Autofabricantes/H3_Henar-3/01_Documentation/H3_Flashing_04.png

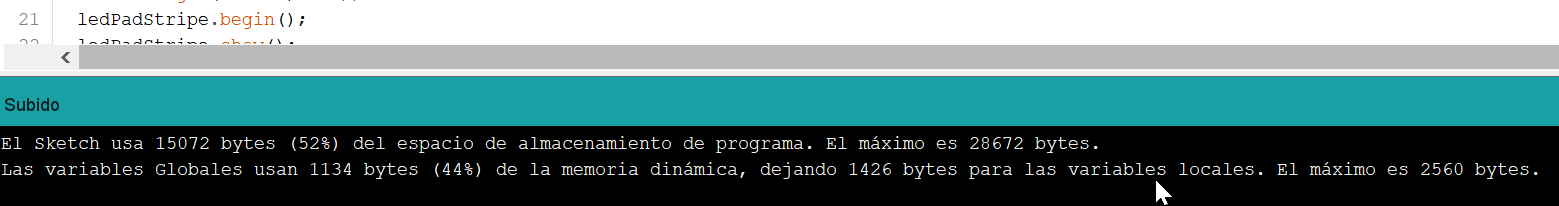
01_Documentation/H3_Flashing_04.png
