Autofabricantes/H3_Henar-3/01_Documentation/H3_Flashing_06.png

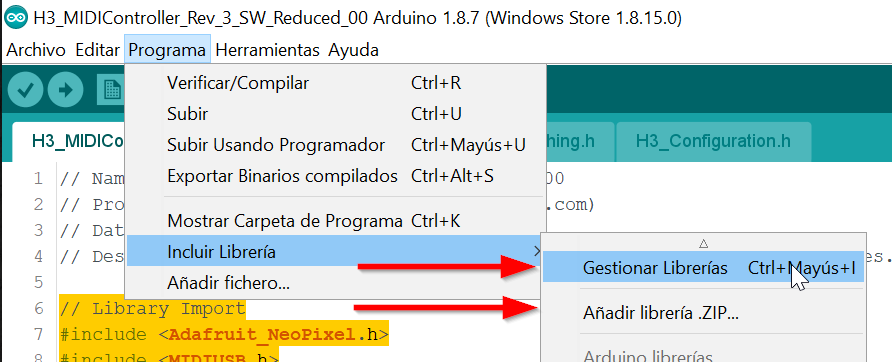
01_Documentation/H3_Flashing_06.png
