Autofabricantes/H3_Henar-3/01_Documentation/H3_REDUCED_00.png

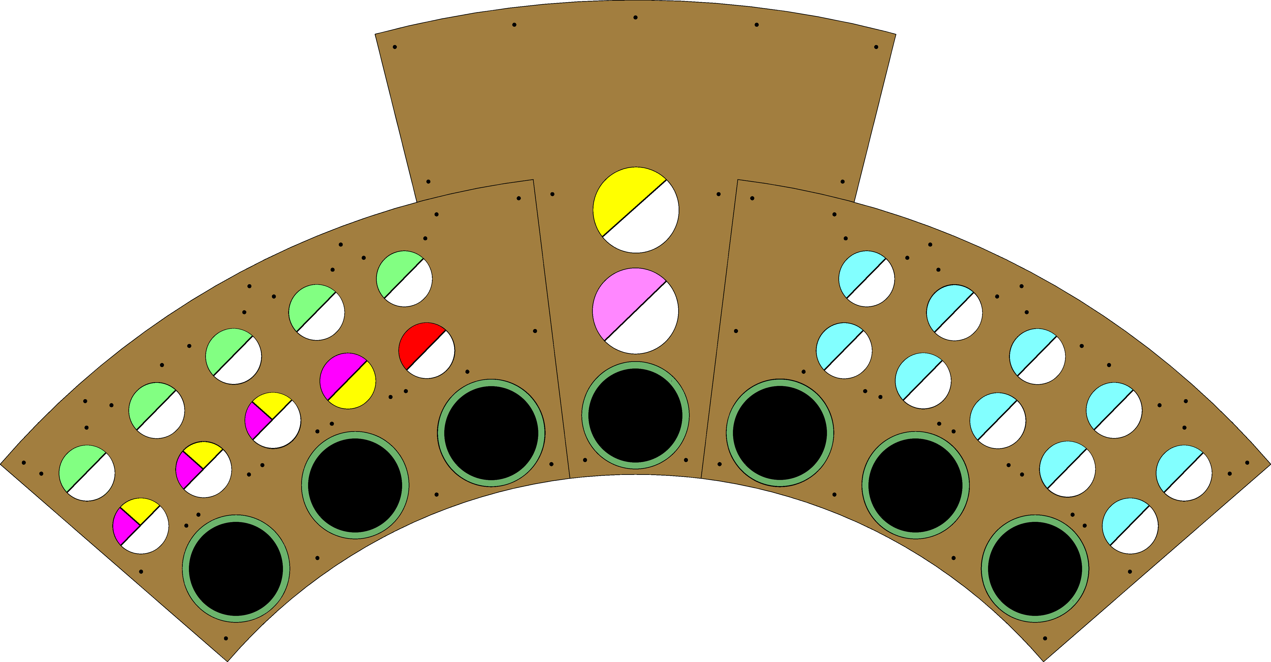
01_Documentation/H3_REDUCED_00.png
