Autofabricantes/H3_Henar-3/01_Documentation/H3_System_Rev_1_Diagram.png

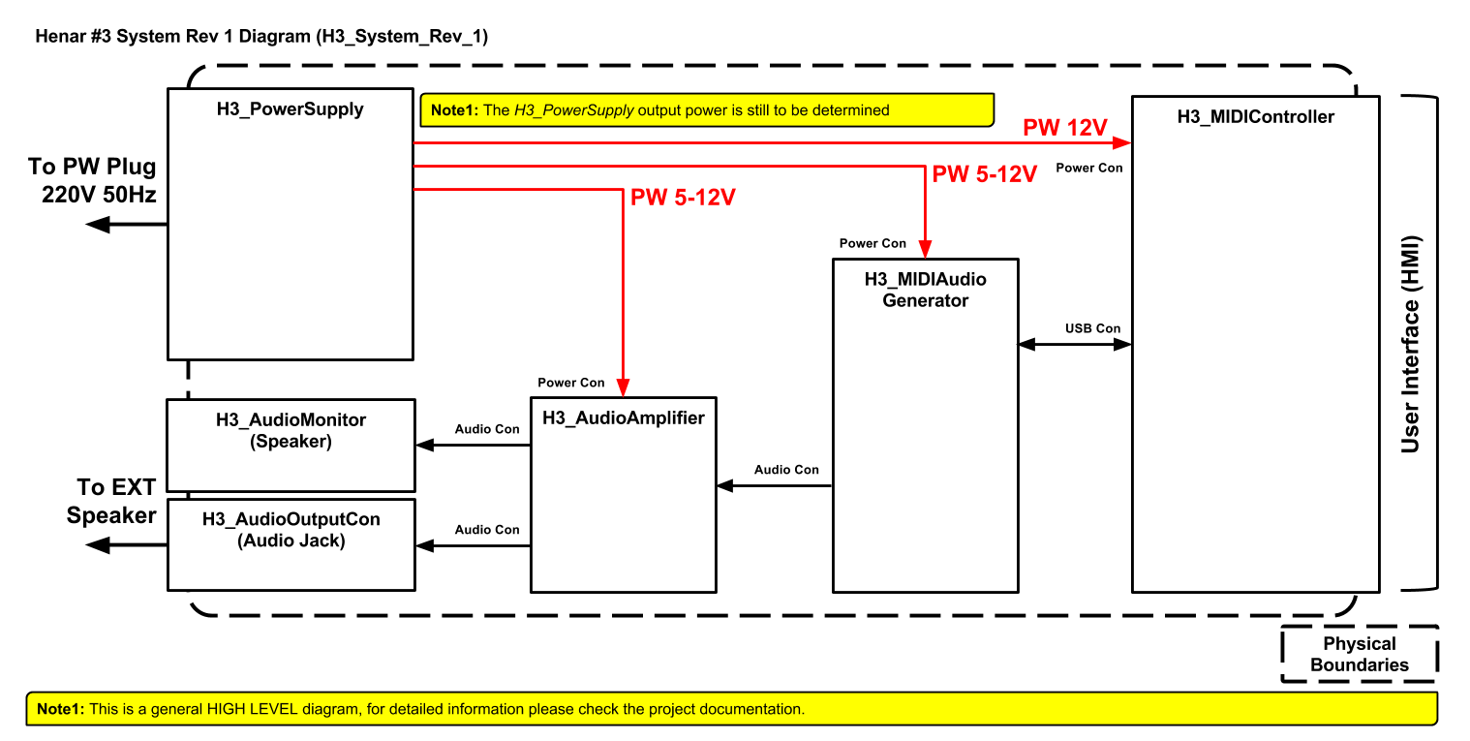
01_Documentation/H3_System_Rev_1_Diagram.png
