Autofabricantes/H3_Henar-3/02_Elements/H3_MIDISmallController_Rev_1/00_Documentation/H3_MIDISmallController_Rev_1_2DRender.png

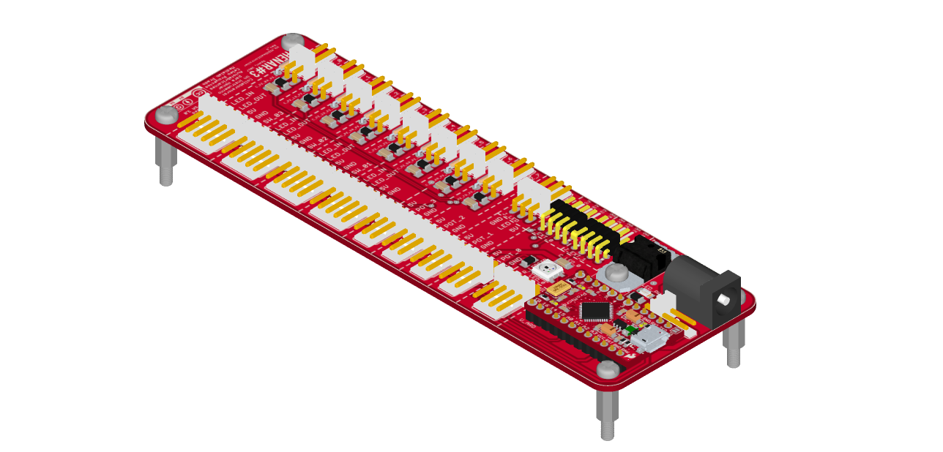
02_Elements/H3_MIDISmallController_Rev_1/00_Documentation/H3_MIDISmallController_Rev_1_2DRender.png
