Autofabricantes/H3_Henar-3/02_Elements/H3_MIDISmallController_Rev_1/01_HW/eagleUp/eagleUp_H3_MIDISmallController_Rev_1_board_top.png

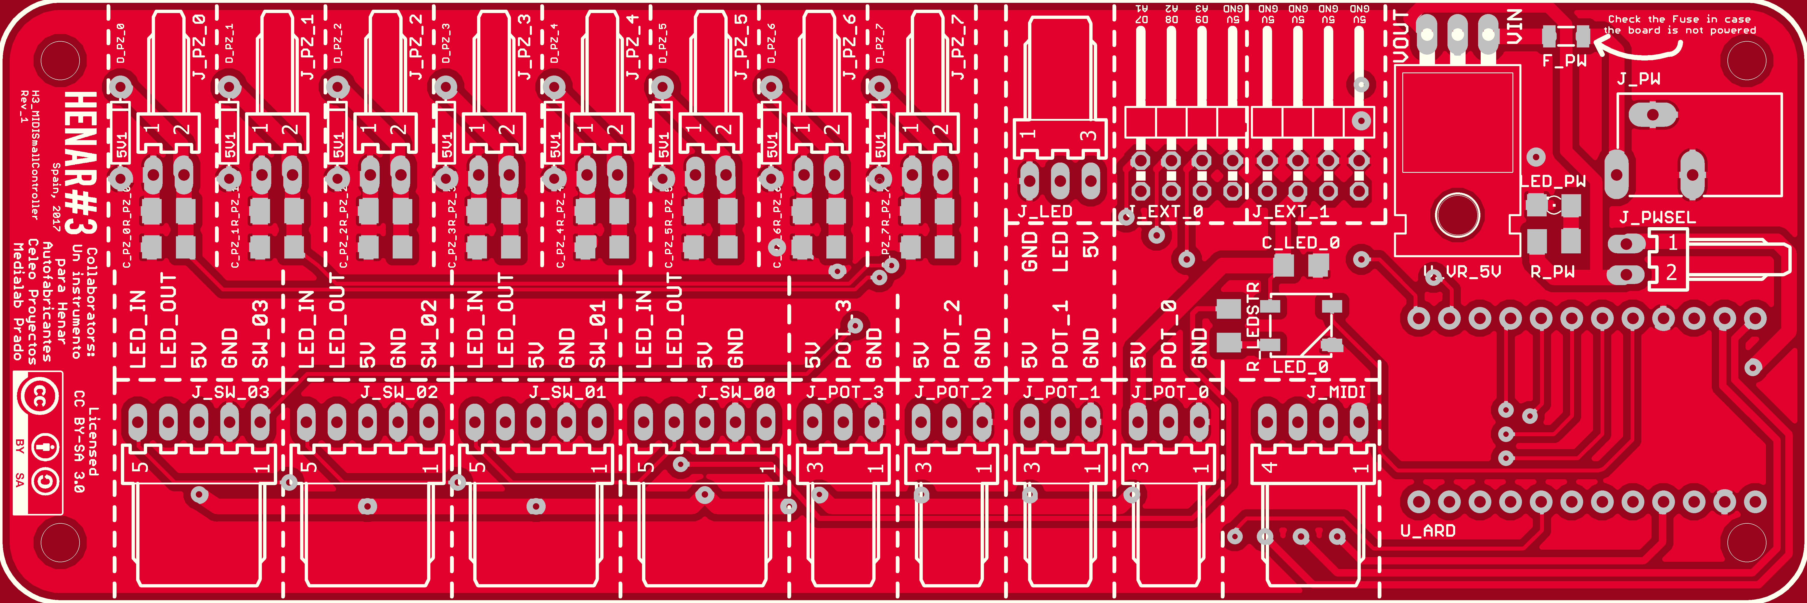
02_Elements/H3_MIDISmallController_Rev_1/01_HW/eagleUp/eagleUp_H3_MIDISmallController_Rev_1_board_top.png
