Autofabricantes/H3_Henar-3/02_Elements/H3_SWPad_Big_Rev_3/00_Documentation/H3_SWPad_Small_Rev_3_Board_Symbol.png

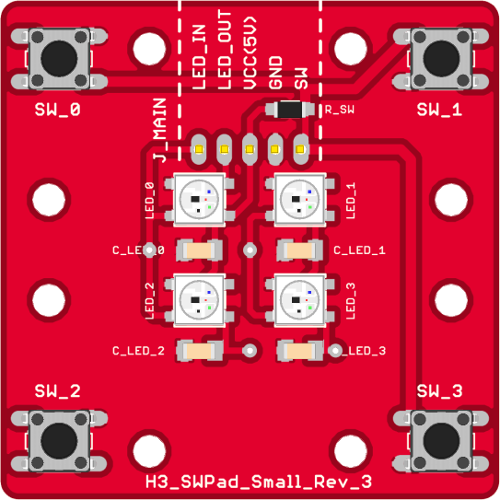
02_Elements/H3_SWPad_Big_Rev_3/00_Documentation/H3_SWPad_Small_Rev_3_Board_Symbol.png
