Autofabricantes/H3_Henar-3/02_Elements/H3_SWPad_Small_Rev_3/01_HW/eagleUp/eagleUp_H3_SWPad_Small_Rev_3_board_top.png

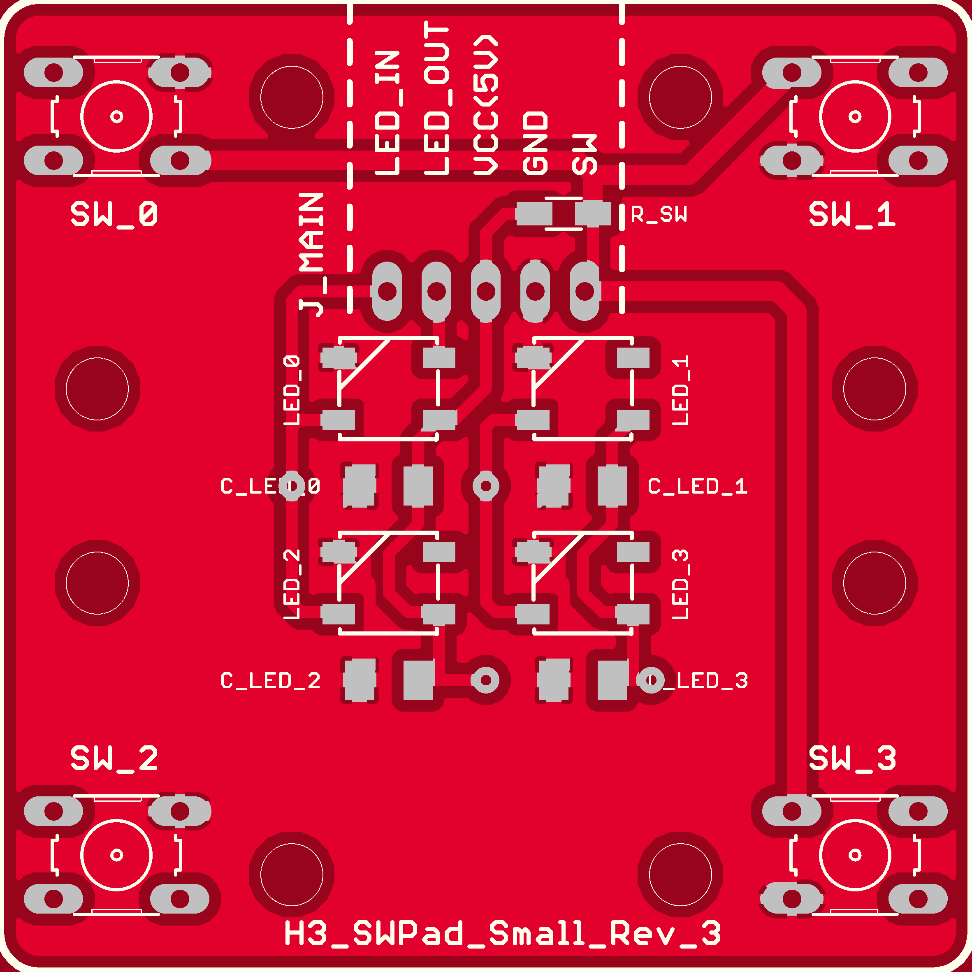
02_Elements/H3_SWPad_Small_Rev_3/01_HW/eagleUp/eagleUp_H3_SWPad_Small_Rev_3_board_top.png
