Autofabricantes/H3_Henar-3/02_Elements/H3_SWPad_Small_Rev_3/01_HW/eagleUp/eagleUp_H3_SWPad_Small_Rev_3_TopMec_board_bottom.png

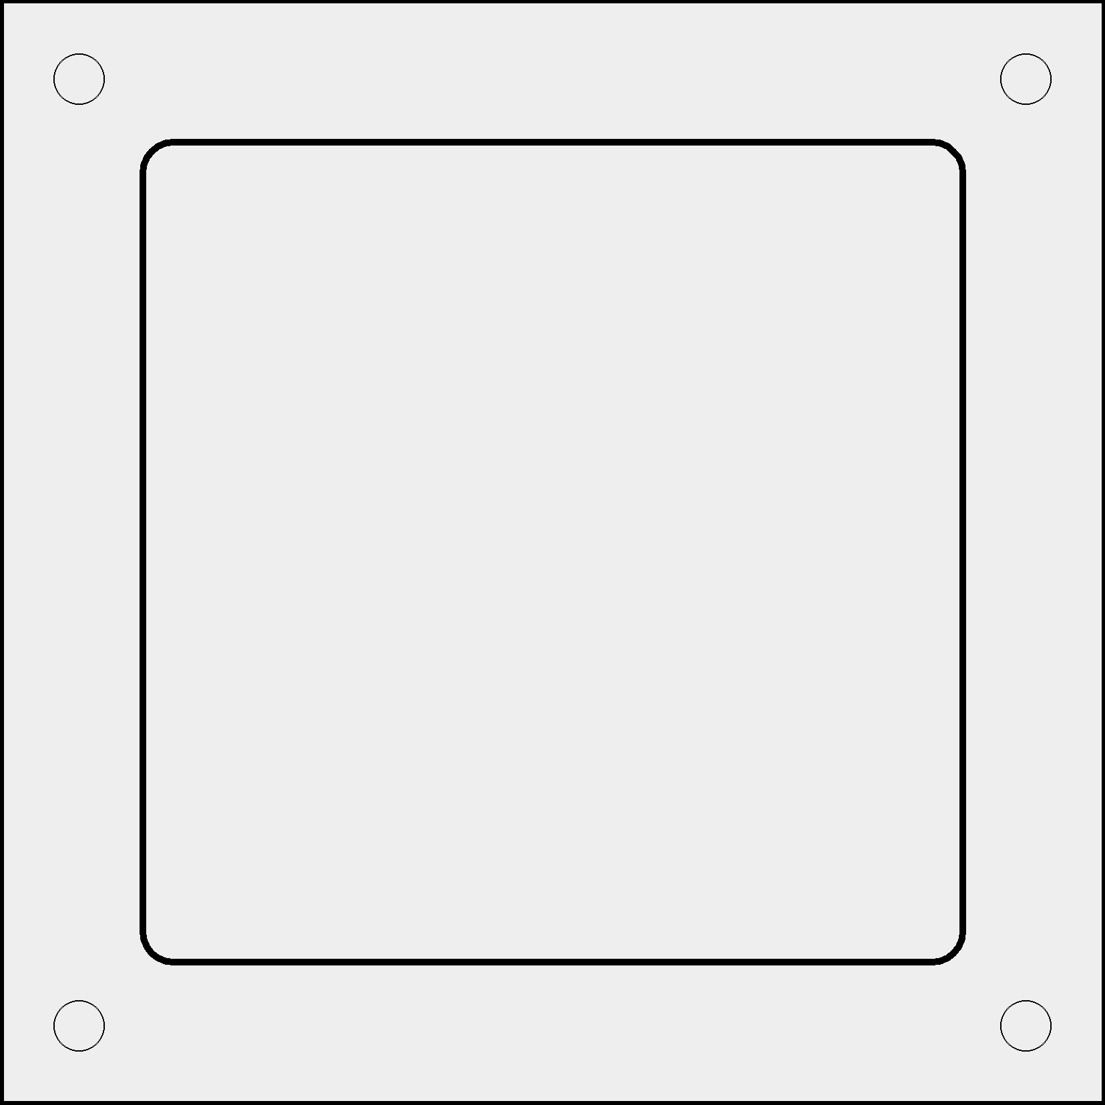
02_Elements/H3_SWPad_Small_Rev_3/01_HW/eagleUp/eagleUp_H3_SWPad_Small_Rev_3_TopMec_board_bottom.png
