Autofabricantes/H3_Henar-3/03_Resources/H3_ComponentImages/H3_MIDISmallController_Rev_1_2DRender_D.png

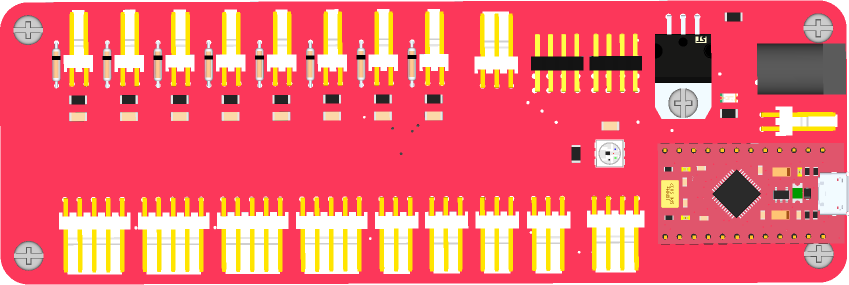
03_Resources/H3_ComponentImages/H3_MIDISmallController_Rev_1_2DRender_D.png
