Autofabricantes/H3_Henar-3/03_Resources/H3_ComponentImages/H3_POTPad_Rev_2_2DRender.png

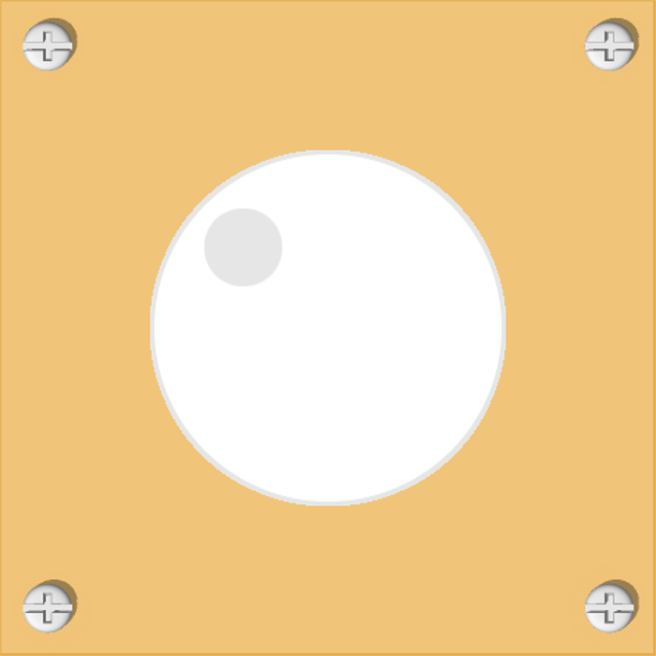
03_Resources/H3_ComponentImages/H3_POTPad_Rev_2_2DRender.png
