Autofabricantes/H3_Henar-3/03_Resources/H3_ComponentImages/H3_SWPad_Small_Rev_3_2DRender.png

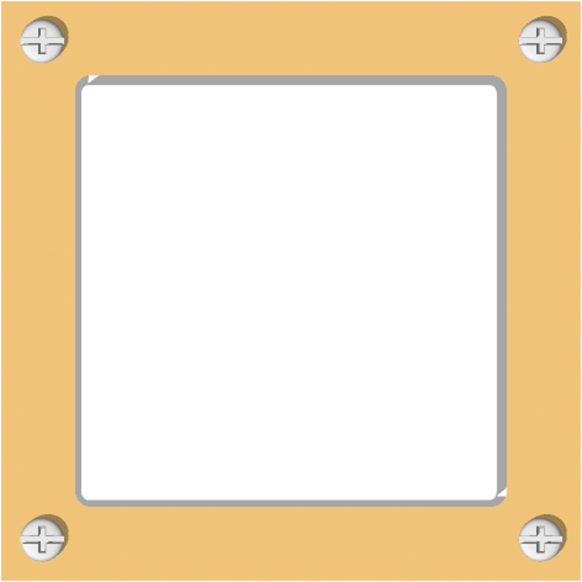
03_Resources/H3_ComponentImages/H3_SWPad_Small_Rev_3_2DRender.png
