Autofabricantes/H3_Henar-3/03_Resources/H3_ComponentImages/SensoresFull.jpg

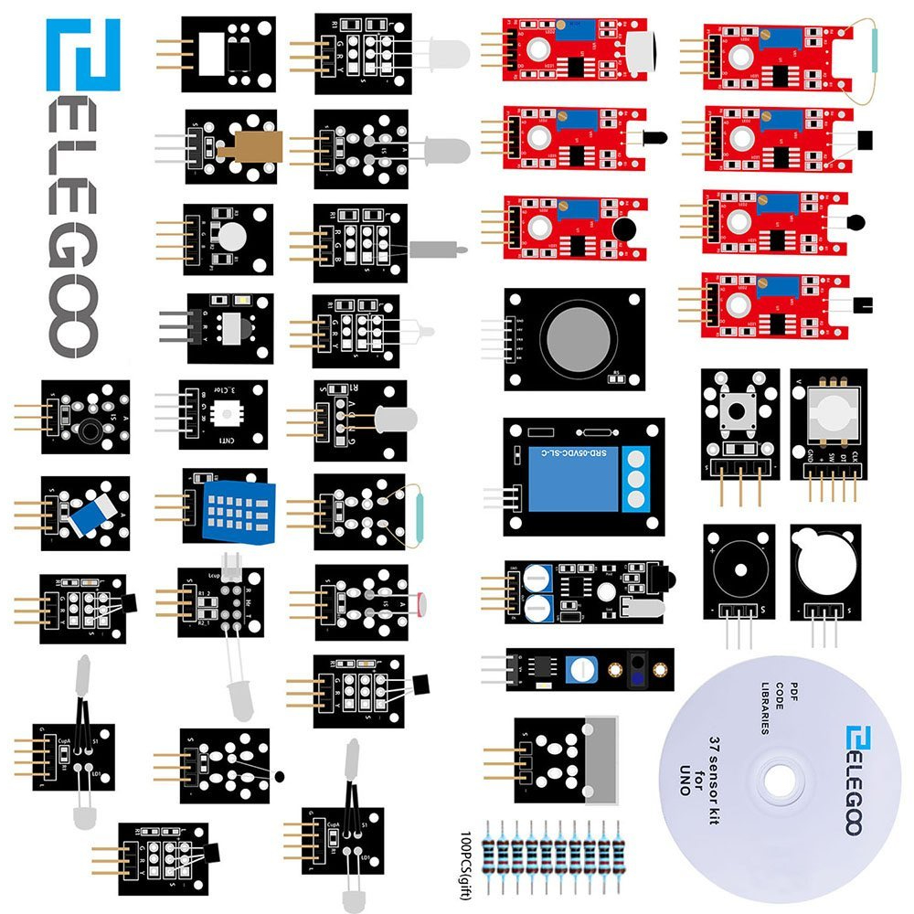
03_Resources/H3_ComponentImages/SensoresFull.jpg
