Autofabricantes/H3_Henar-3/01_Documentation/H3_GuideResources/H3_PAD_Render/H3_PAD_FRST_ON.png

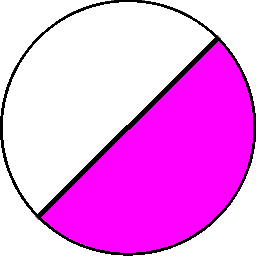
01_Documentation/H3_GuideResources/H3_PAD_Render/H3_PAD_FRST_ON.png
