Autofabricantes/H3_Henar-3/01_Documentation/H3_GuideResources/H3_SET_Render/H3_SLEEP.png

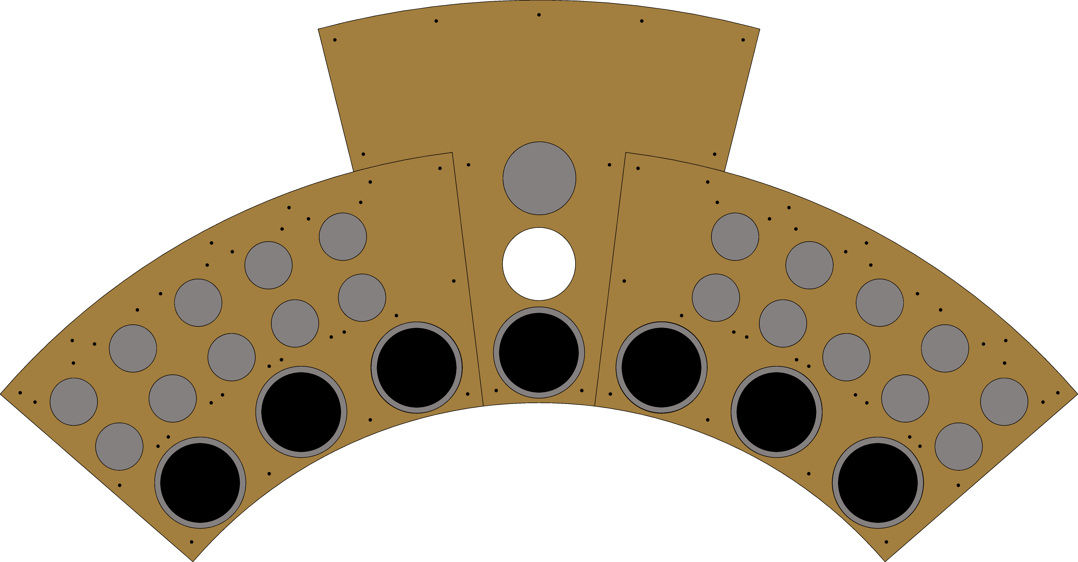
01_Documentation/H3_GuideResources/H3_SET_Render/H3_SLEEP.png
