Autofabricantes/H3_Henar-3/02_Elements/H3_VelostatPadTest/00_Documentation/H3_VelostatTest (1).png

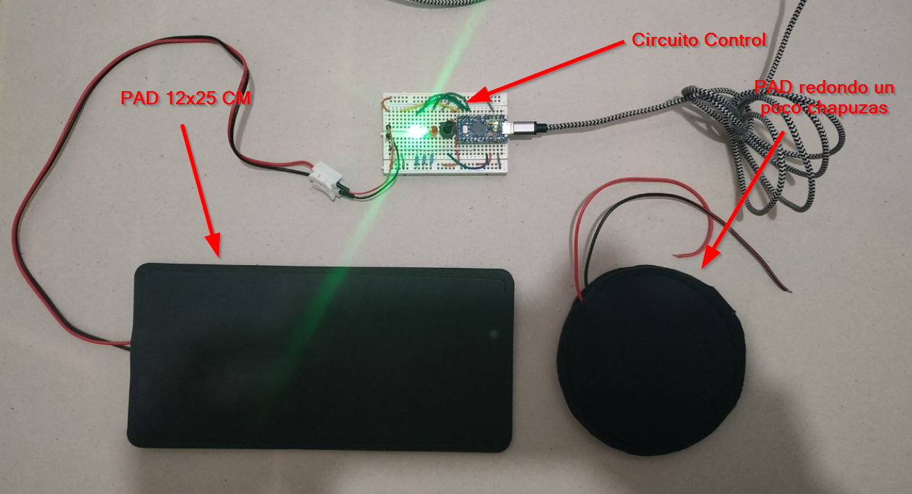
02_Elements/H3_VelostatPadTest/00_Documentation/H3_VelostatTest (1).png
