Autofabricantes/H3_Henar-3/02_Elements/H3_VelostatPadTest/00_Documentation/H3_VelostatTest (2).png

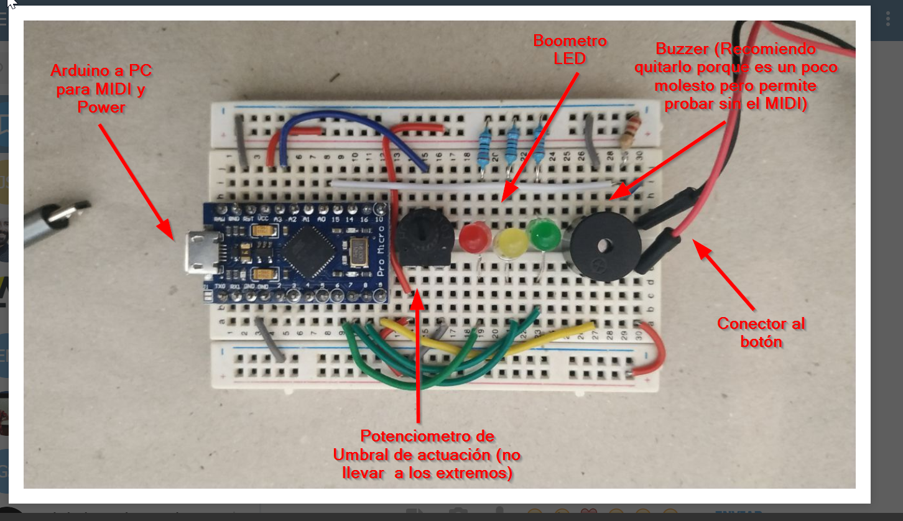
02_Elements/H3_VelostatPadTest/00_Documentation/H3_VelostatTest (2).png
