Autofabricantes/H3_Henar-3/03_Resources/H3_VelostatExperiment/H3_VelostatExperiment_00.jpg

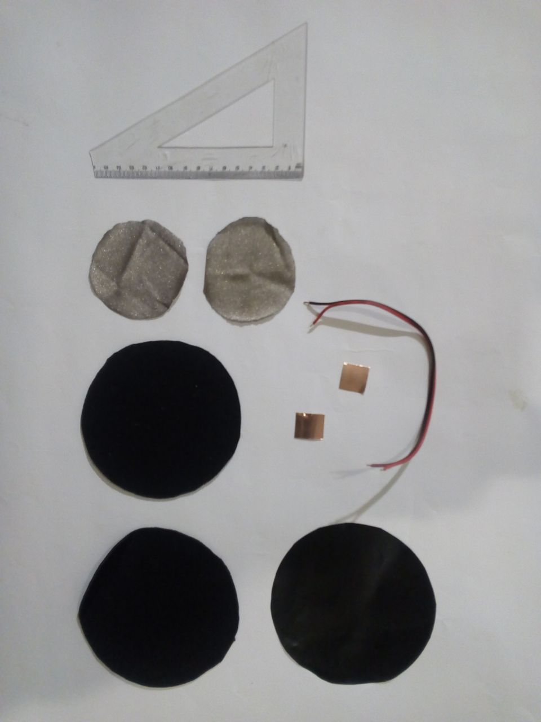
03_Resources/H3_VelostatExperiment/H3_VelostatExperiment_00.jpg
