Autofabricantes/H3_Henar-3/02_Elements/H3_SWPad_Small_Rev_2/00_Documentation/H3_SWPad_Small_Rev_2_Schematic.pdf

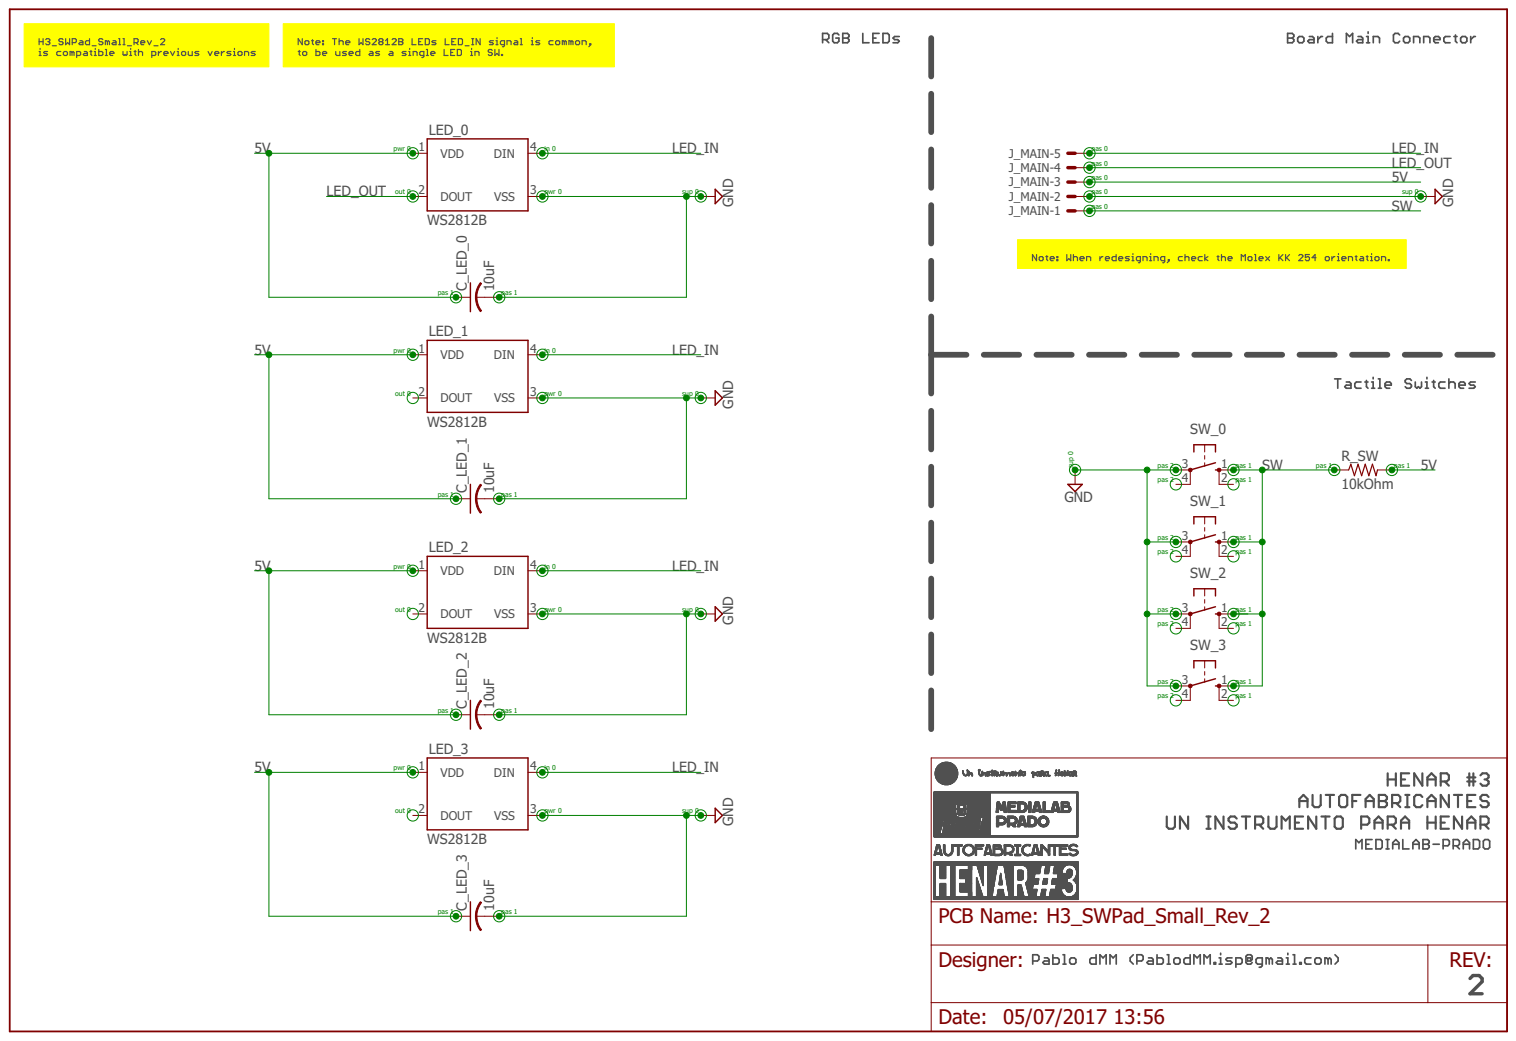
[picture p71: page 1]
