Autofabricantes/H3_Henar-3/02_Elements/H3_MIDIController_Rev_1_MainBoard/00_Documentation/H3_MIDIController_Rev_1_MainBoard_Schematic.pdf

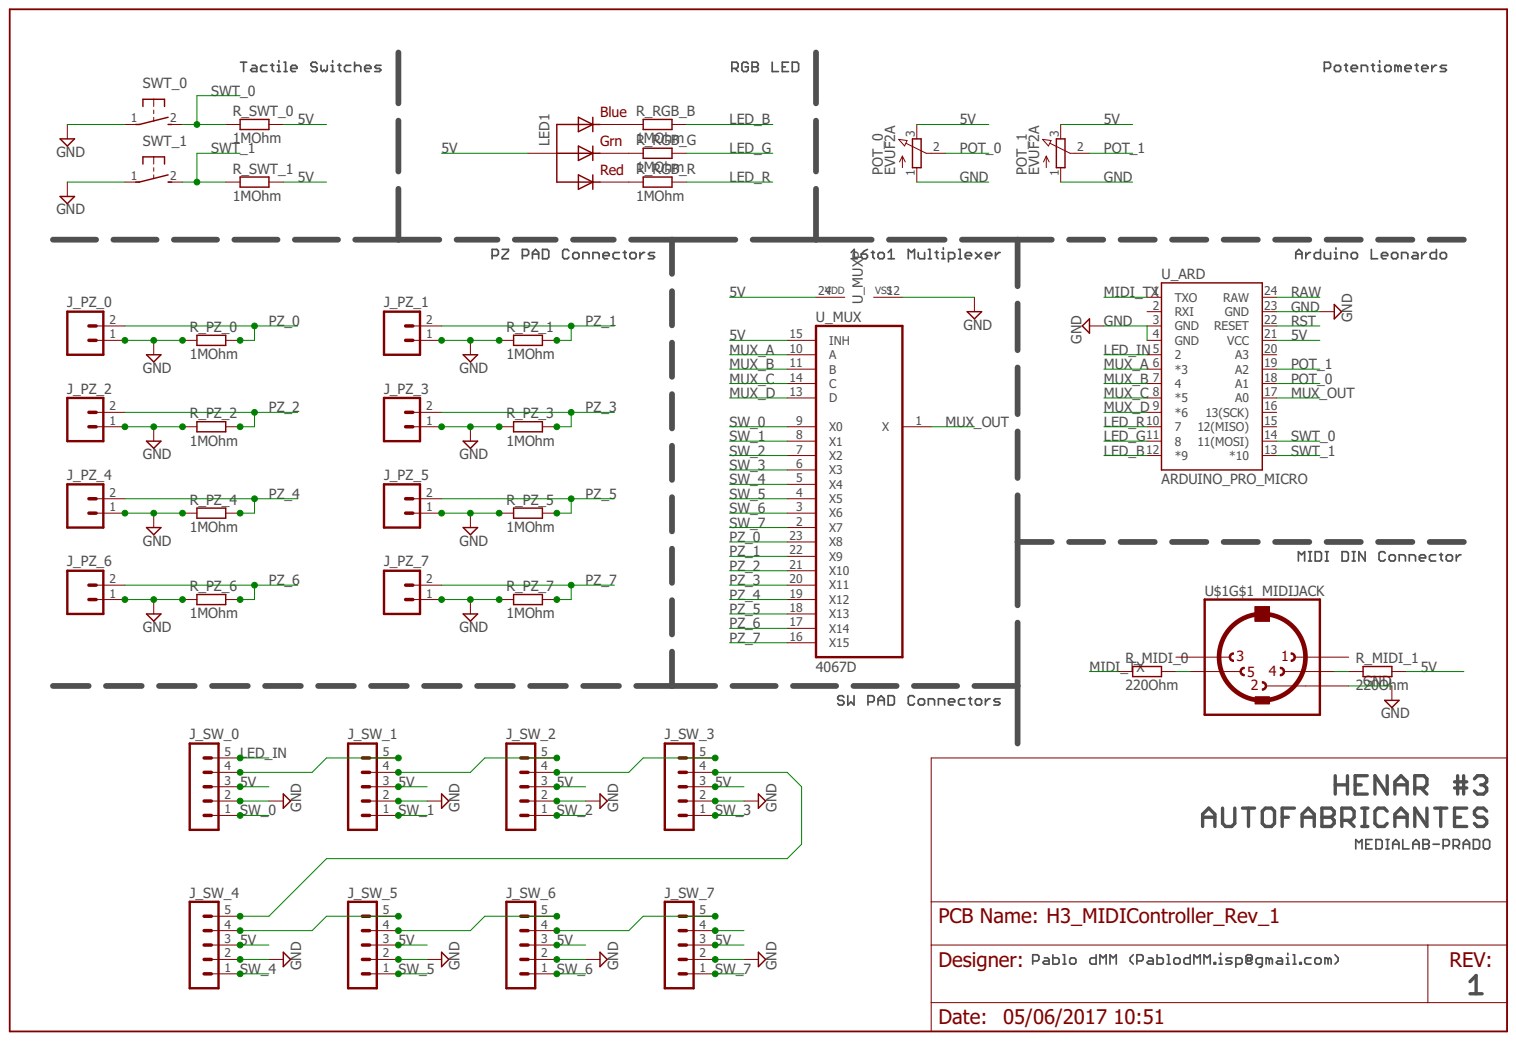
[picture p72: page 1]
