Autofabricantes/H3_Henar-3/02_Elements/H3_MIDIController_Rev_2_MainBoard/00_Documentation/H3_MIDIController_Rev_2_MainBoard_Schematic.pdf

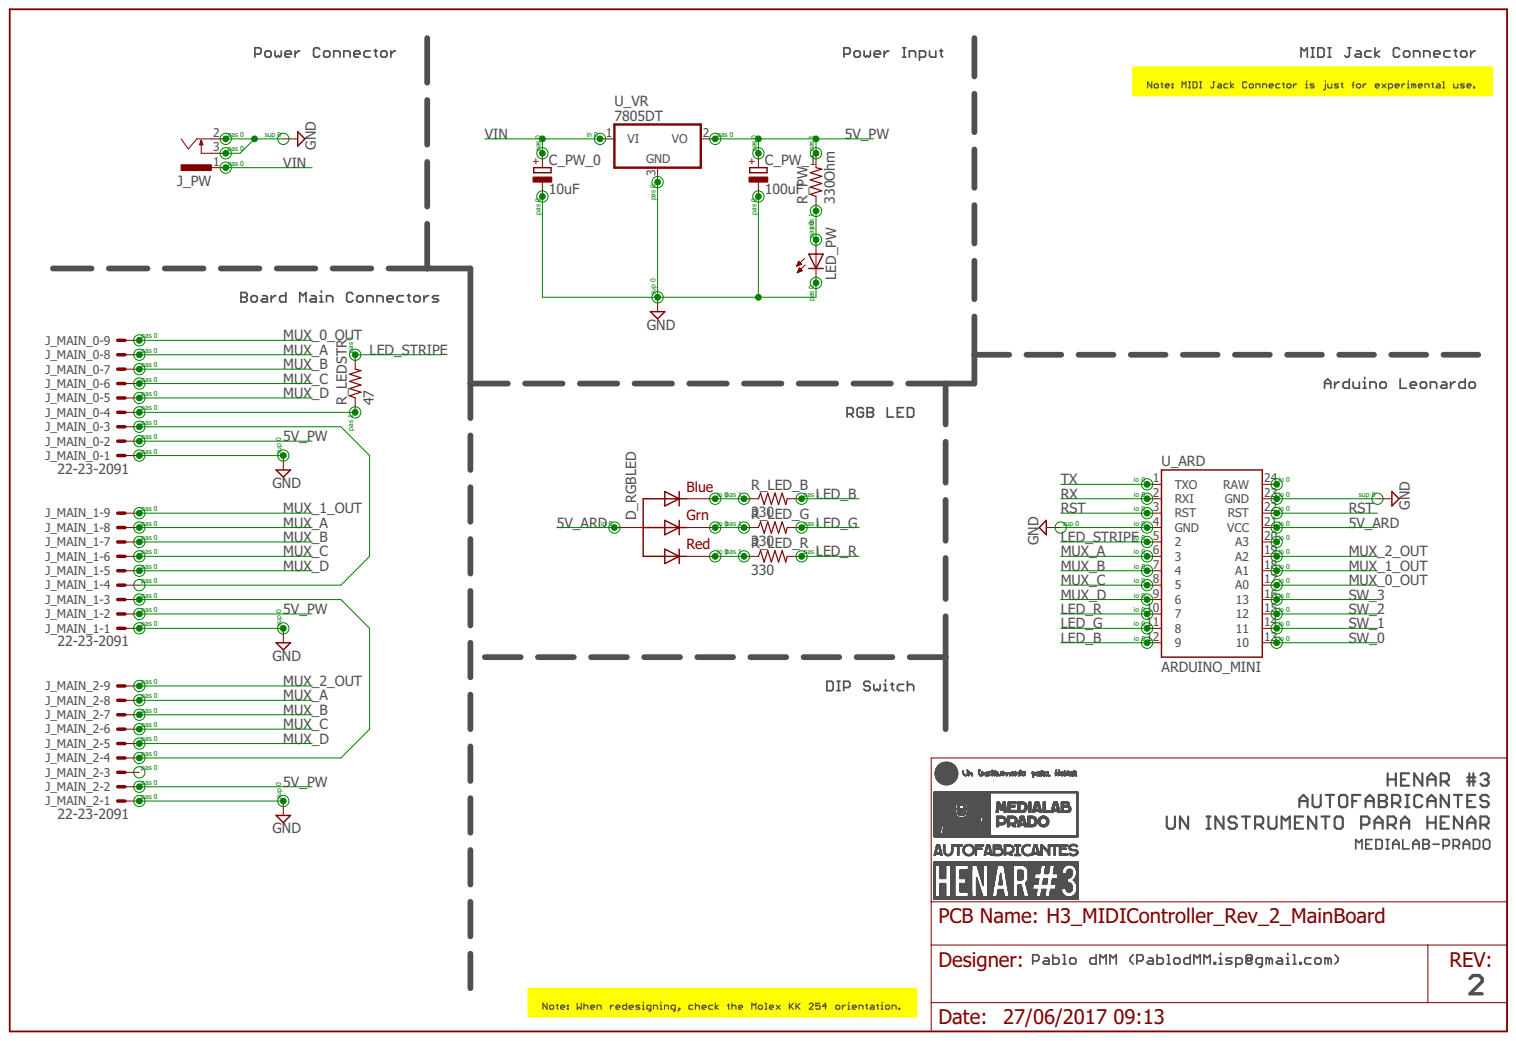
[picture p73: page 1]

pas 0 pas 0 pas 1 pas

pas 0 pas 0 pas 0 pas 0 pas 0 pas 0 pas 0 pas 0 pas 0
