Autofabricantes/H3_Henar-3/02_Elements/H3_SWPad_Small_Rev_1/trunk/H3_HMI_PulsadorSmall_A_Rev_1_TOP.pdf

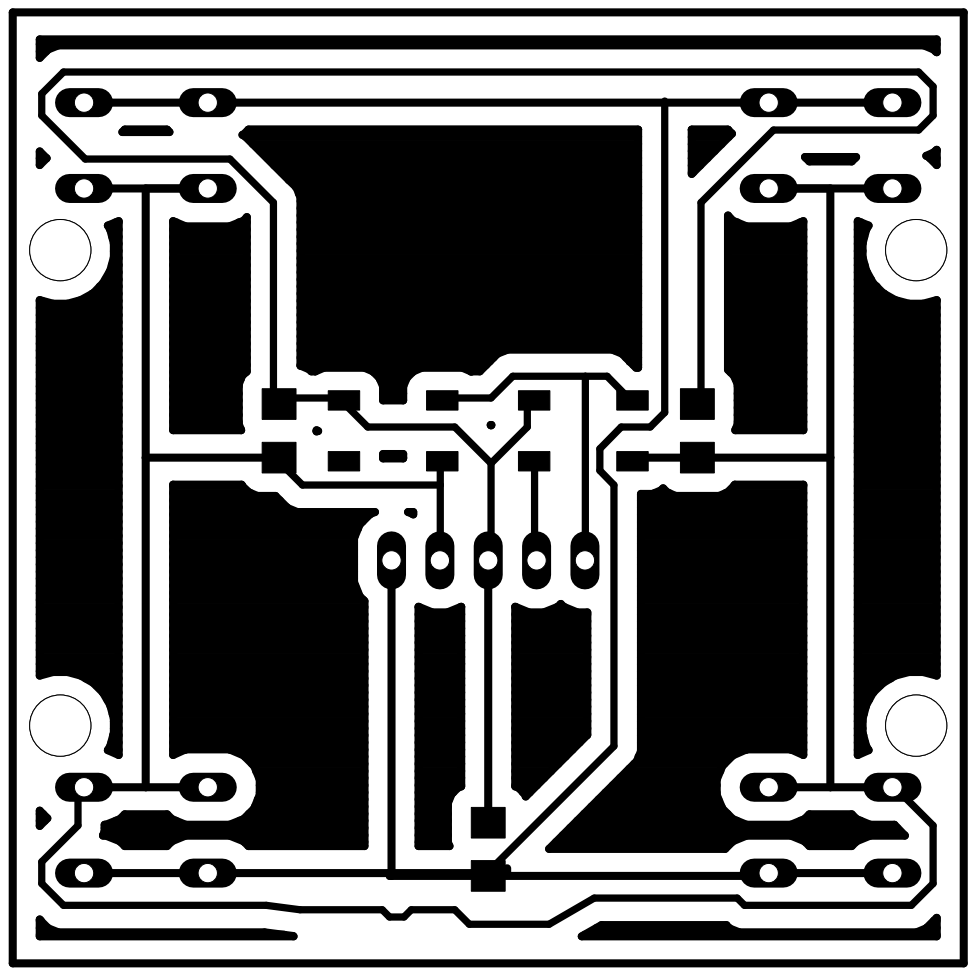
[picture p75: page 1]
