Autofabricantes/H3_Henar-3/02_Elements/H3_SWPad_Small_Rev_2/01_HW/H3_SWPad_Small_Rev_2_Layout_BOT.pdf

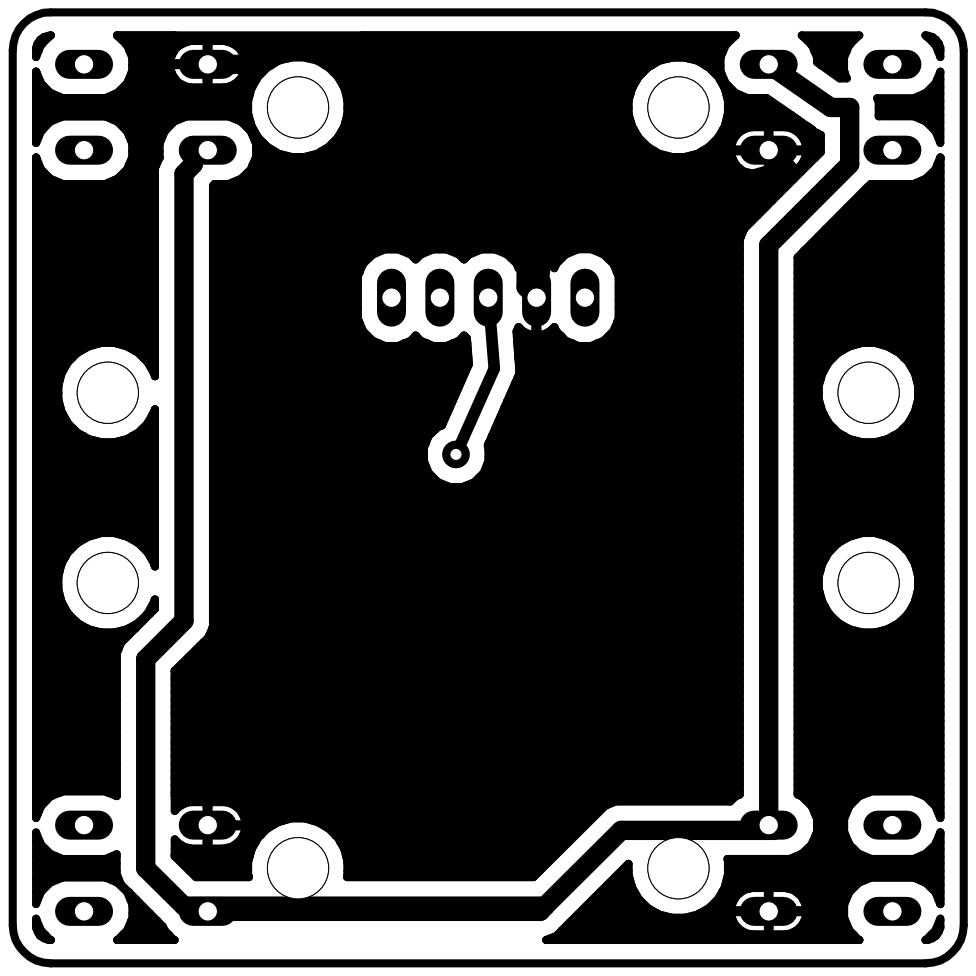
[picture p76: page 1]
